weimanc/game-boy-zero-link-case/stepfiles/game-boy-zero-link-case-screen_frame_petg_long.stl

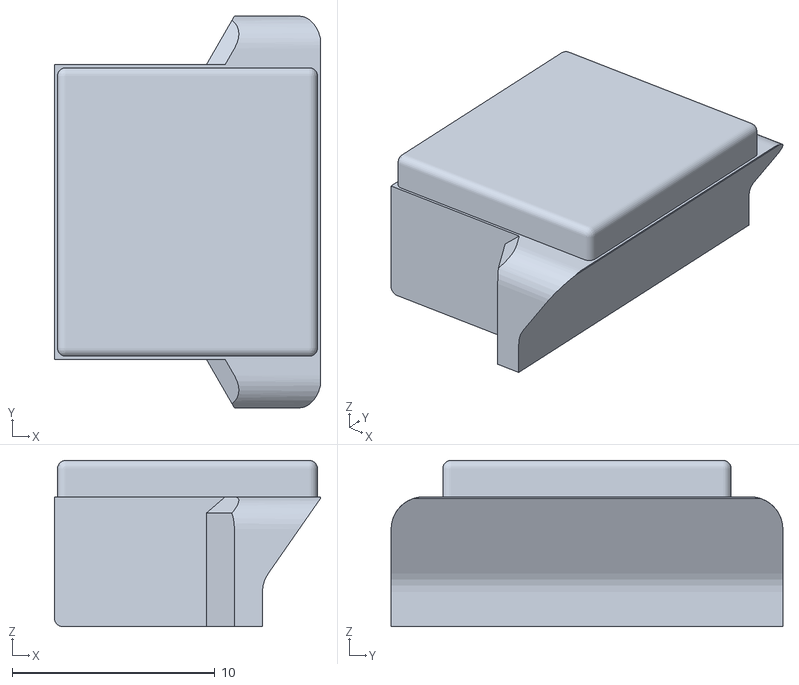
[picture p15: CAD file, 2024-05-06]
stepfiles/game-boy-zero-link-case-screen_frame_petg_long.stl
13.1 x 19.3 x 8.20
