weimanc/game-boy-zero-link-case/references/gbobj_screen.obj

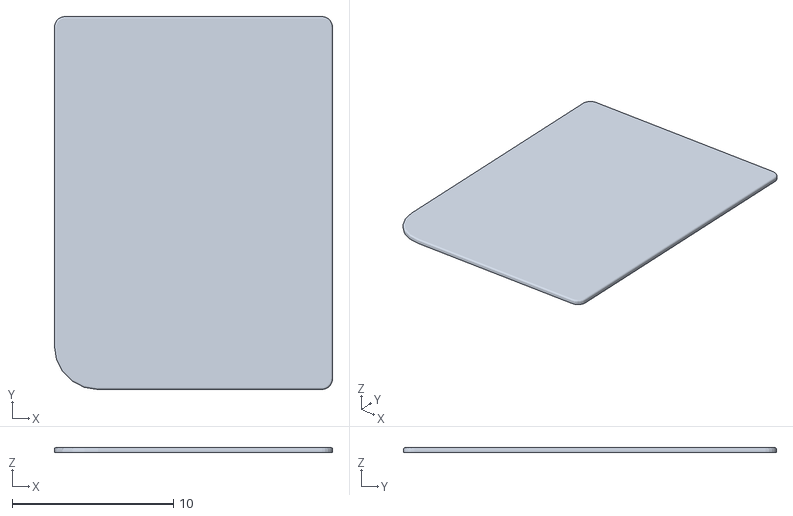
[picture p16: CAD file, 2024-05-04]
references/gbobj_screen.obj
17.3 x 23.1 x 0.315
